ThomasDieckmann/TPL-II/photos/20220920_143919.jpg

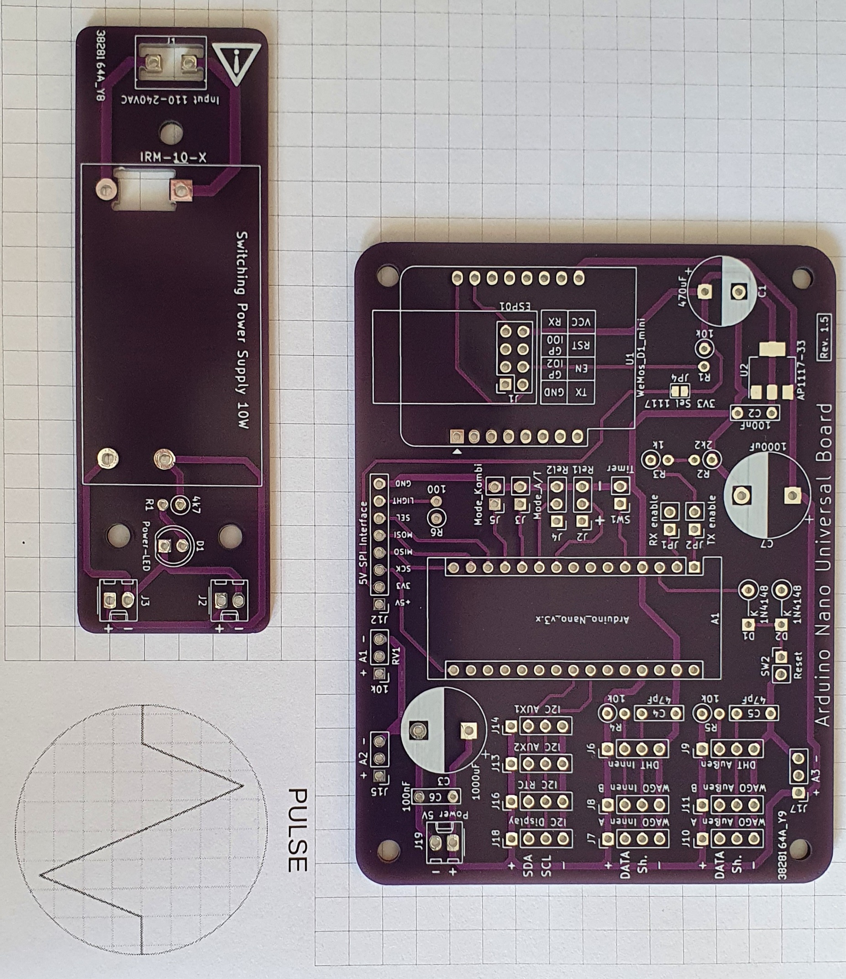
photos/20220920_143919.jpg
