ThomasDieckmann/TPL-II/photos/20221005_145727.jpg

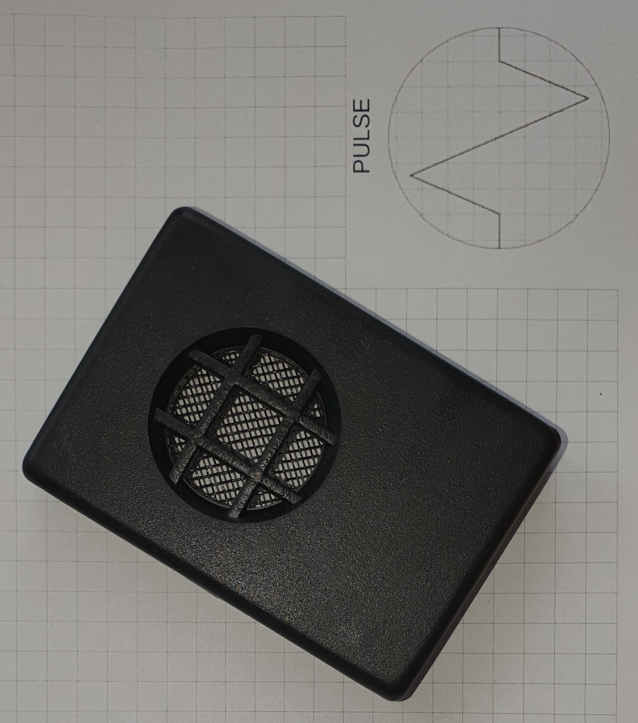
photos/20221005_145727.jpg
