ThomasDieckmann/TPL-II/photos/20221005_145737.jpg

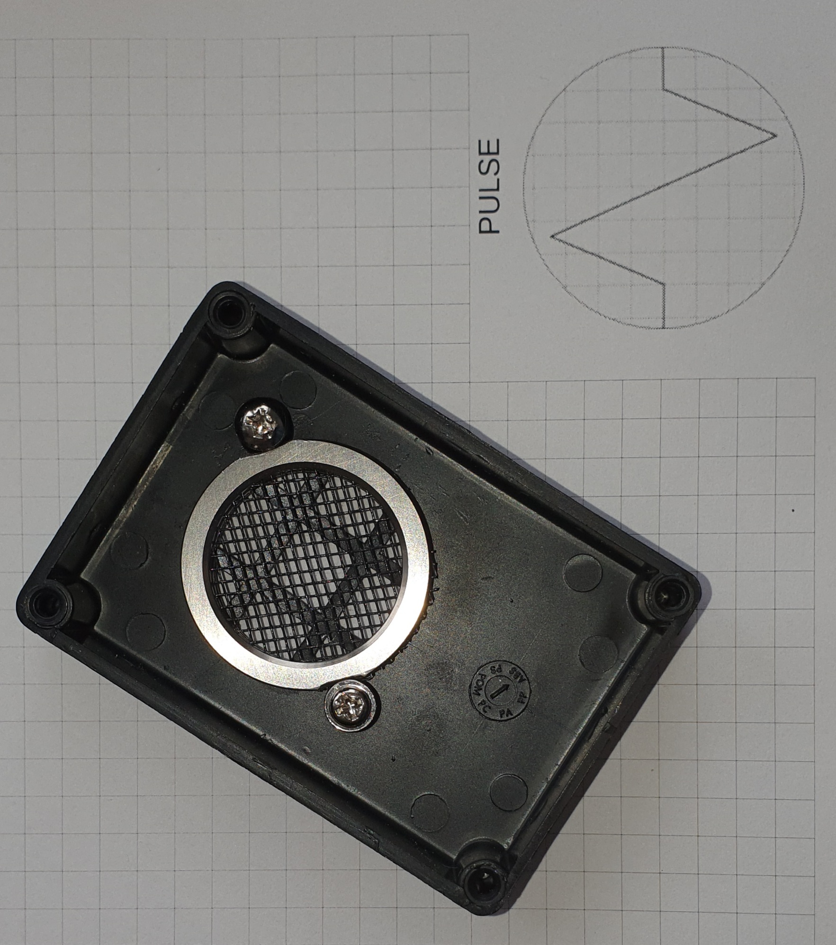
photos/20221005_145737.jpg
