ThomasDieckmann/TPL-II/photos/20221005_145815.jpg

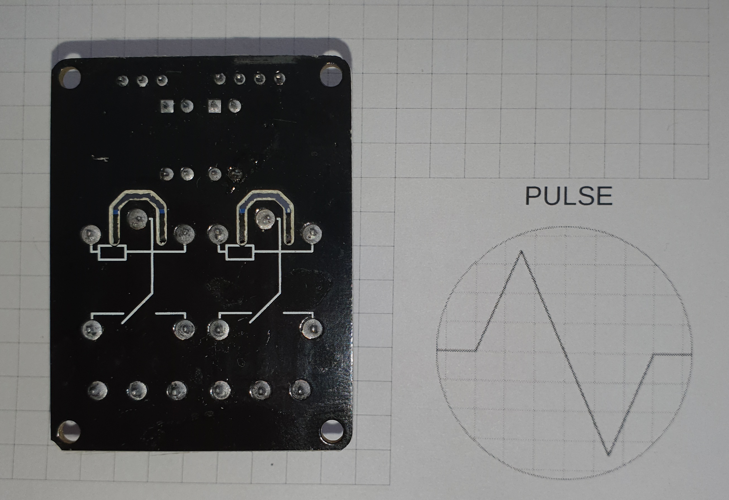
photos/20221005_145815.jpg
