ThomasDieckmann/TPL-II/photos/20221005_145848.jpg

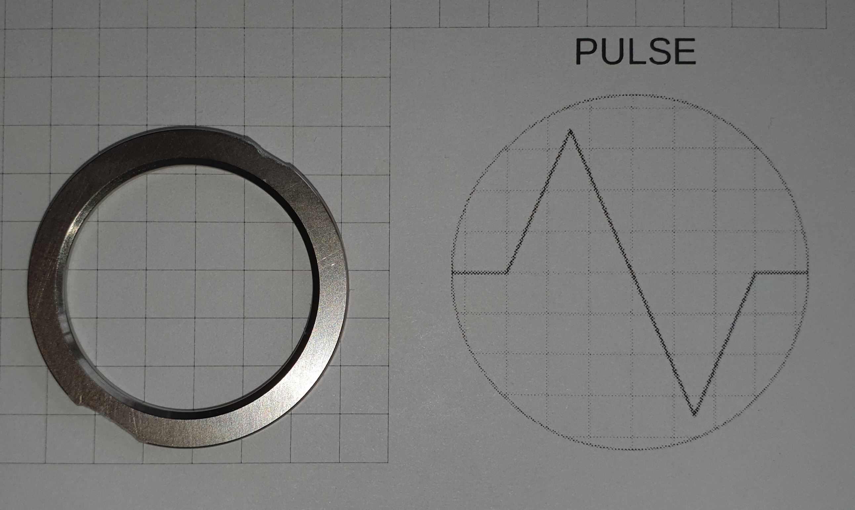
photos/20221005_145848.jpg
