ThomasDieckmann/TPL-II/photos/20221005_151055.jpg

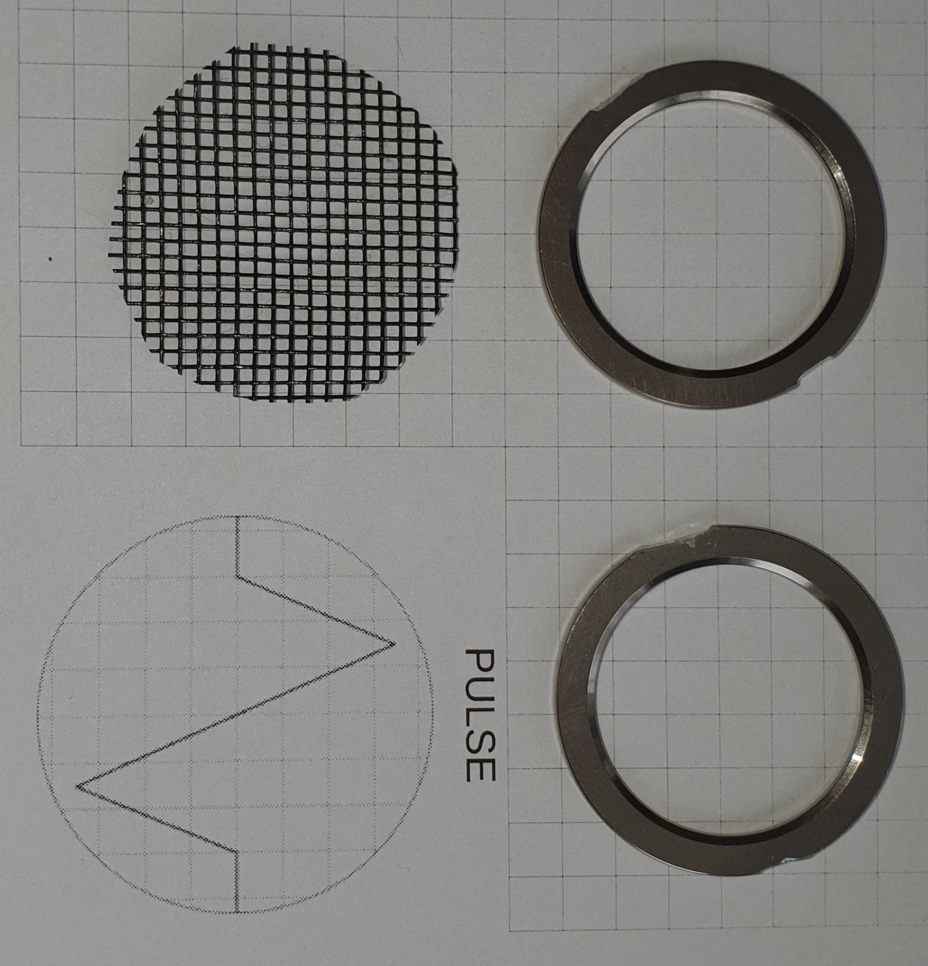
photos/20221005_151055.jpg
