ThomasDieckmann/TPL-II/photos/20221005_151303.jpg

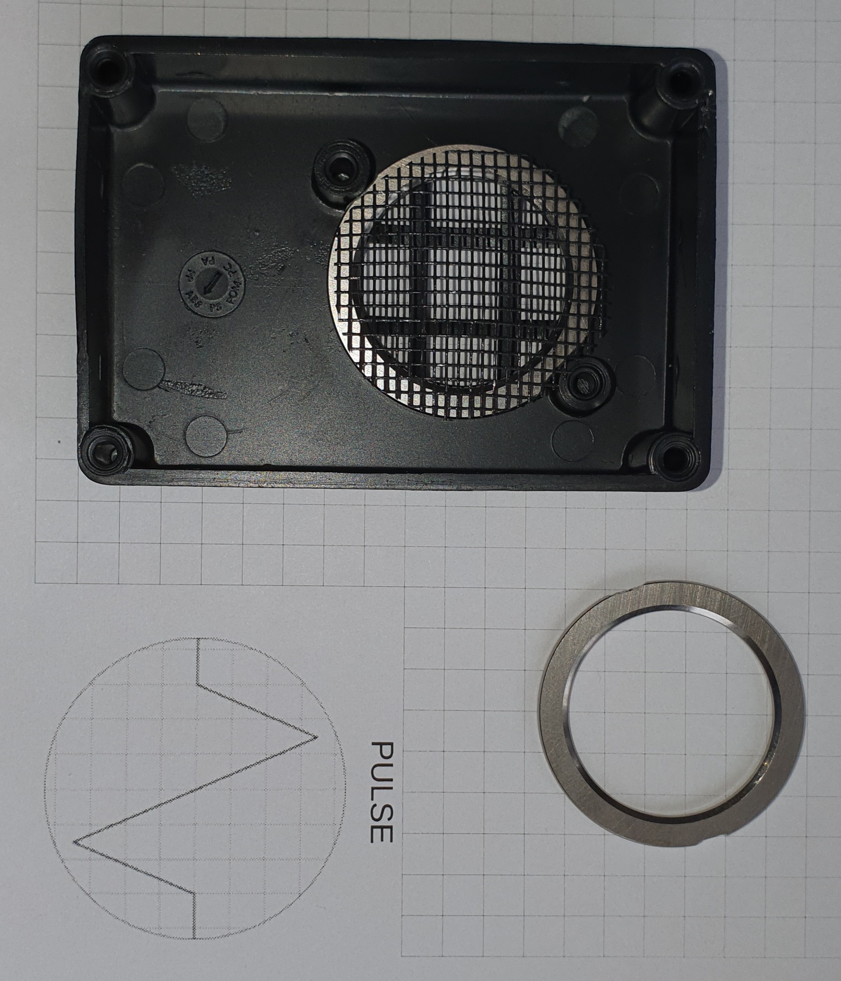
photos/20221005_151303.jpg
