ThomasDieckmann/TPL-II/photos/20221006_083249.jpg

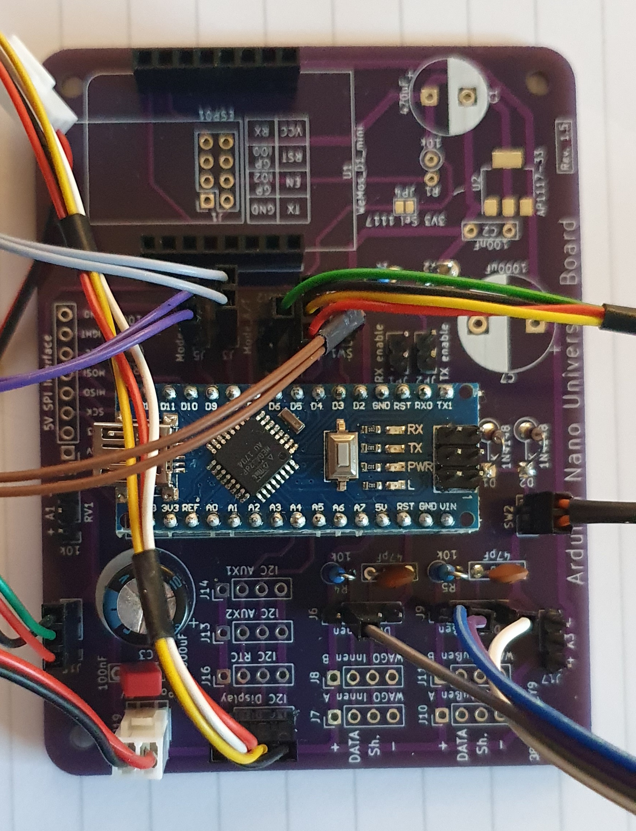
photos/20221006_083249.jpg
