ThomasDieckmann/TPL-II/photos/20221006_105342.jpg

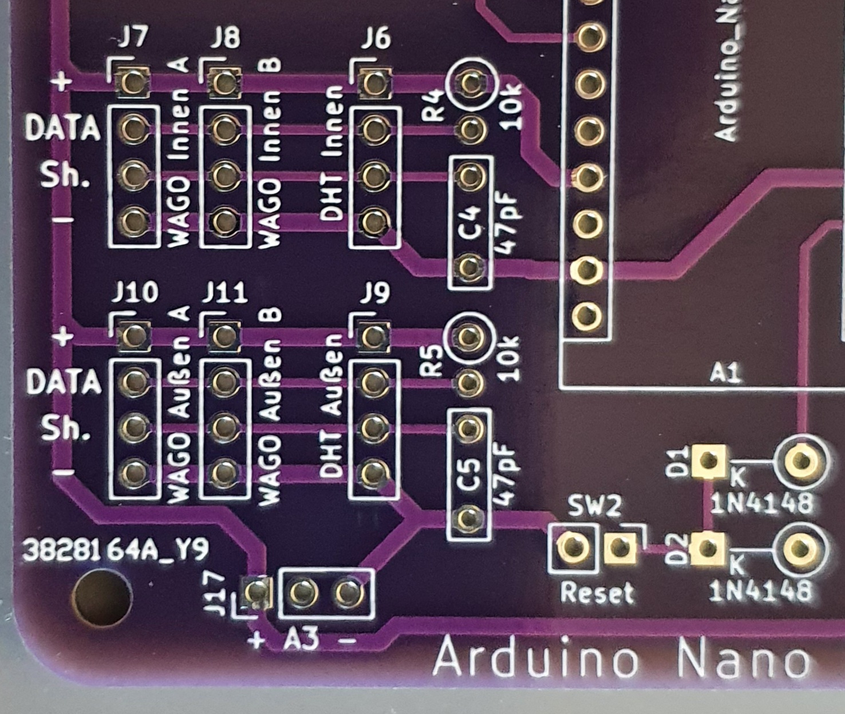
photos/20221006_105342.jpg
