ThomasDieckmann/TPL-II/photos/20221011_225733.jpg

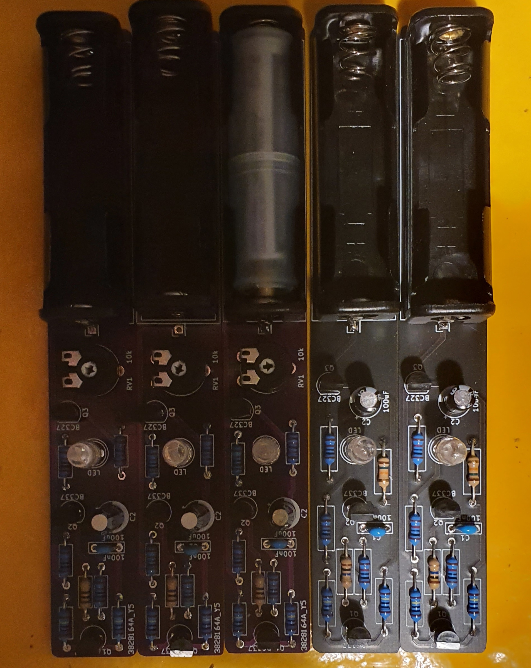
photos/20221011_225733.jpg
