ThomasDieckmann/TPL-II/photos/20221021_124702.jpg

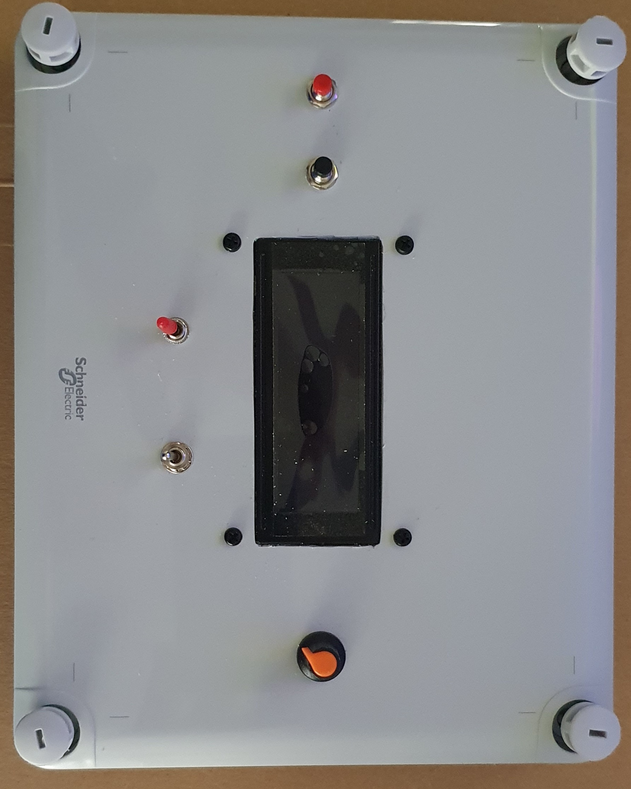
photos/20221021_124702.jpg
