ThomasDieckmann/TPL-II/photos/20221021_125103.jpg

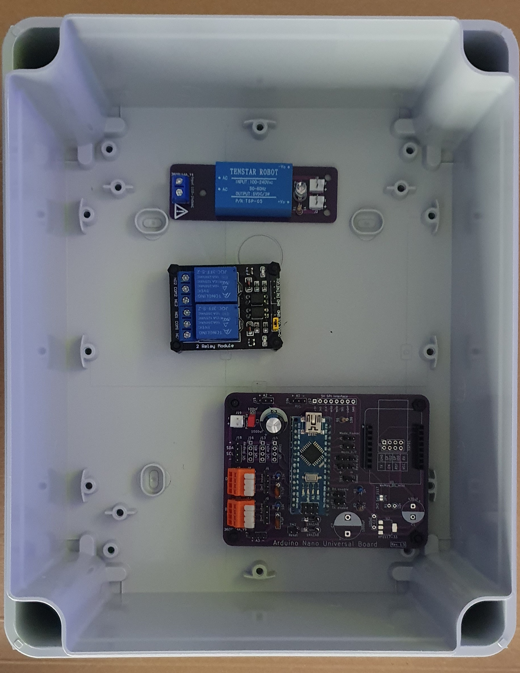
photos/20221021_125103.jpg
