ThomasDieckmann/TPL-II/photos/20221021_145954.jpg

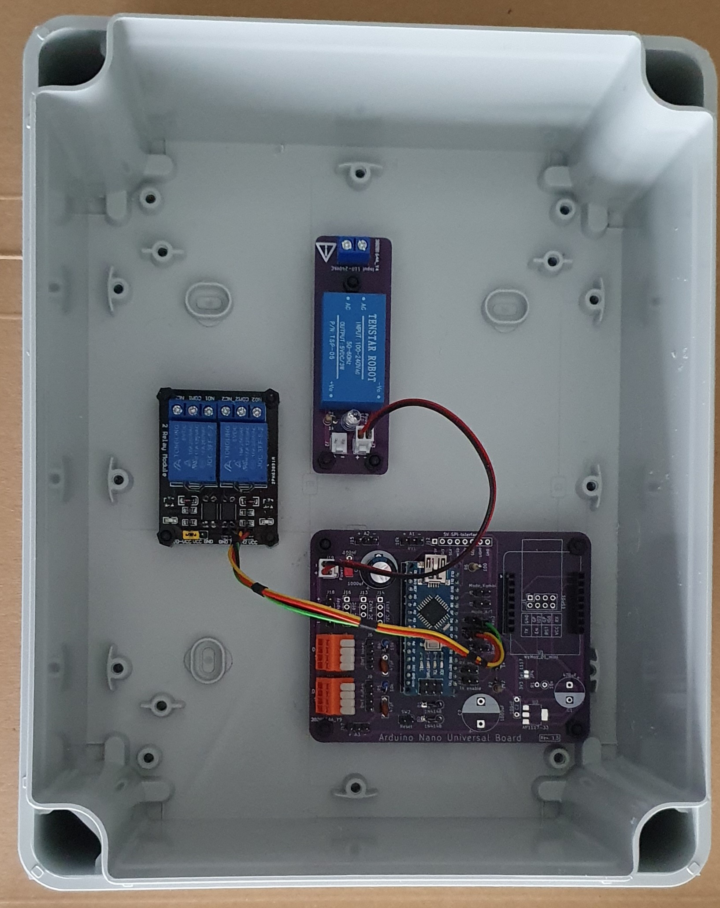
photos/20221021_145954.jpg
