ThomasDieckmann/TPL-II/photos/20221021_170227.jpg

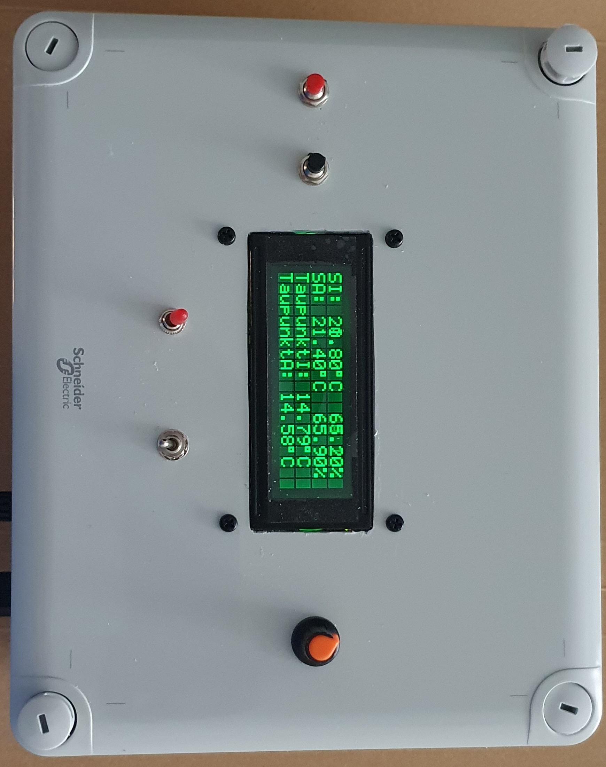
photos/20221021_170227.jpg
