ThomasDieckmann/TPL-II/photos/20221021_170622.jpg

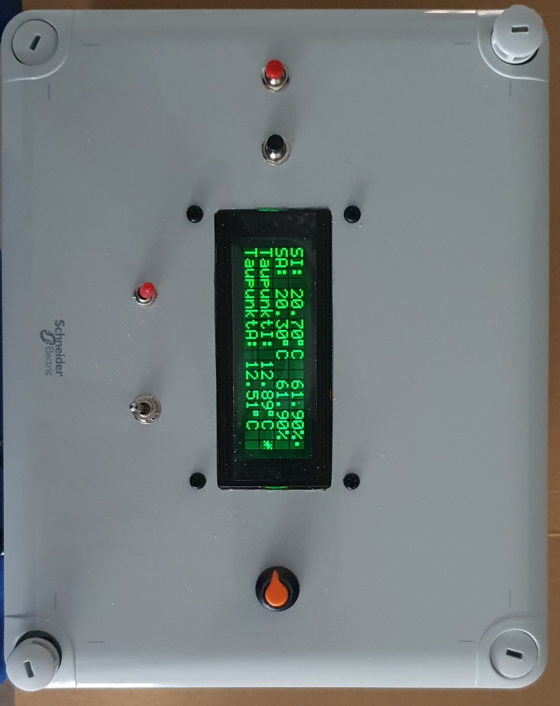
photos/20221021_170622.jpg
