ThomasDieckmann/TPL-II/photos/20221027_135438.jpg

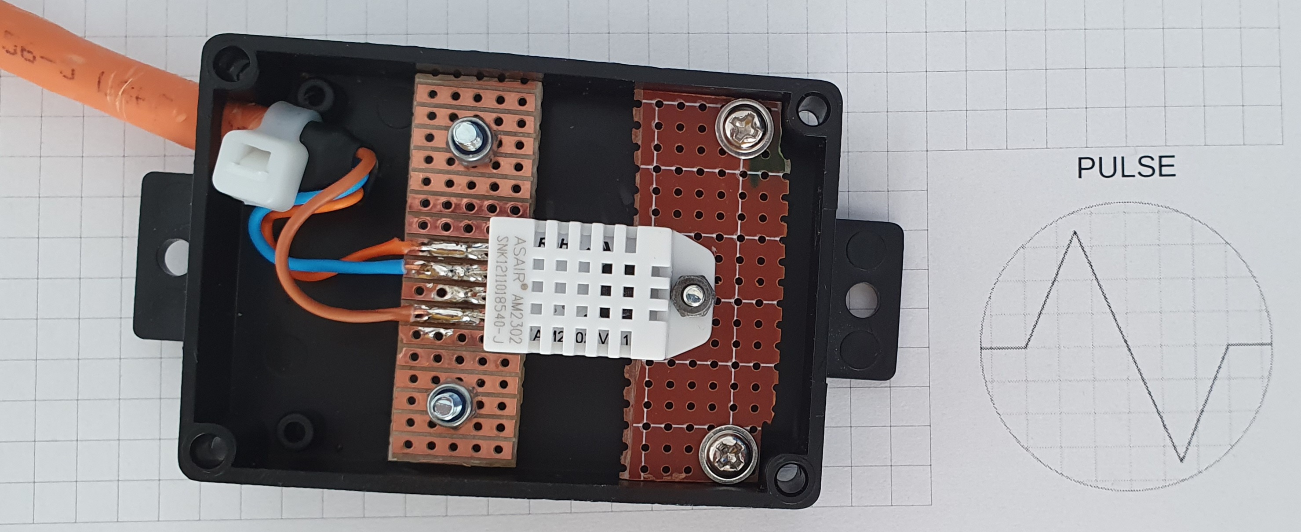
photos/20221027_135438.jpg
