ThomasDieckmann/TPL-II/photos/20221027_141711.jpg

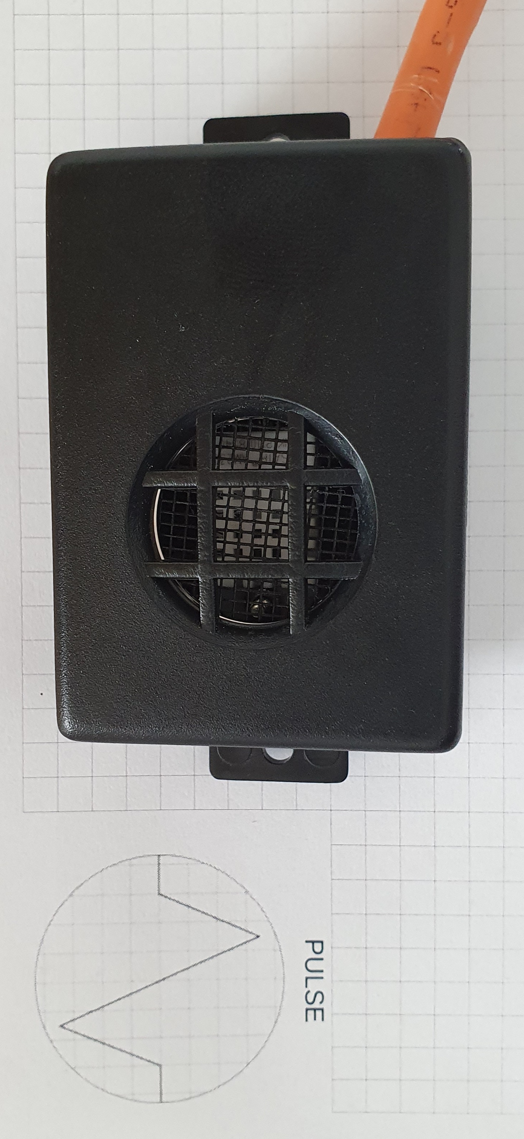
photos/20221027_141711.jpg
