ThomasDieckmann/TPL-II/photos/20221027_153632.jpg

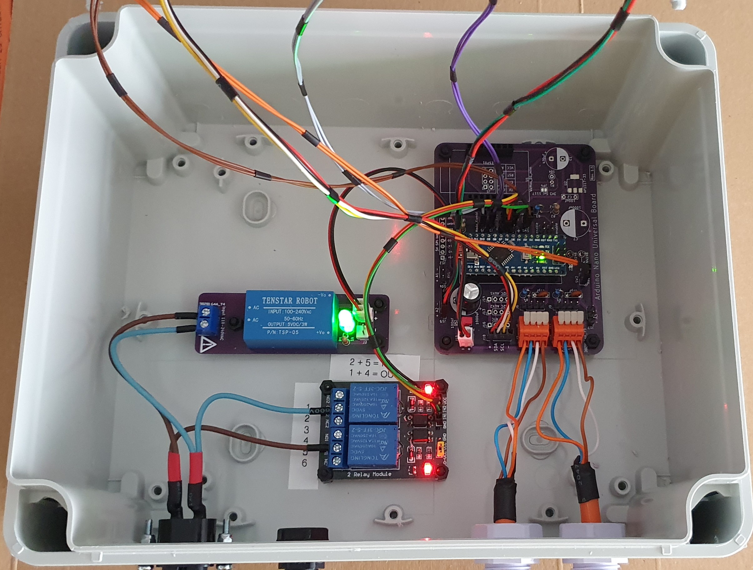
photos/20221027_153632.jpg
