ThomasDieckmann/TPL-II/photos/20221123_121524.jpg

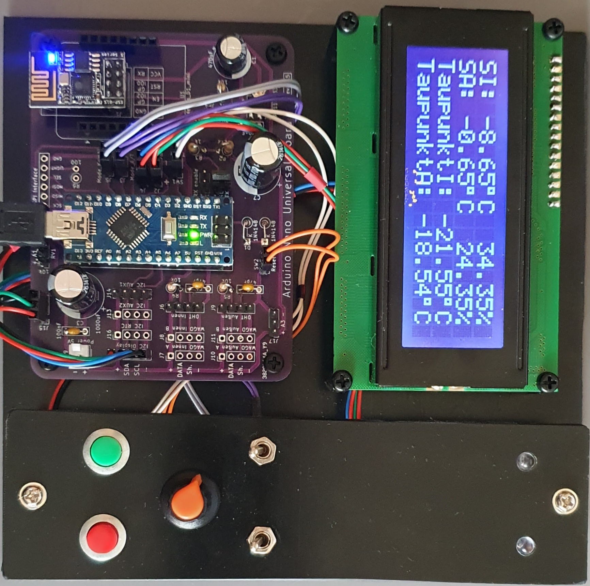
photos/20221123_121524.jpg
