ThomasDieckmann/TPL-II/photos/20231001_195801.jpg

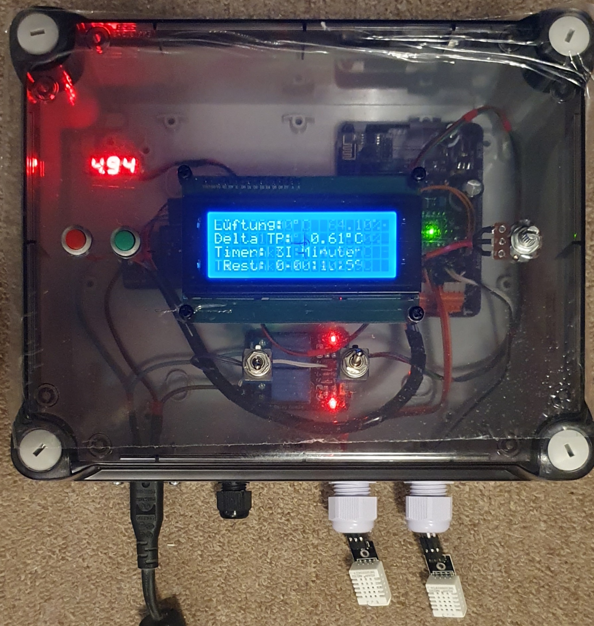
photos/20231001_195801.jpg
