ThomasDieckmann/TPL-II/photos/board.jpg

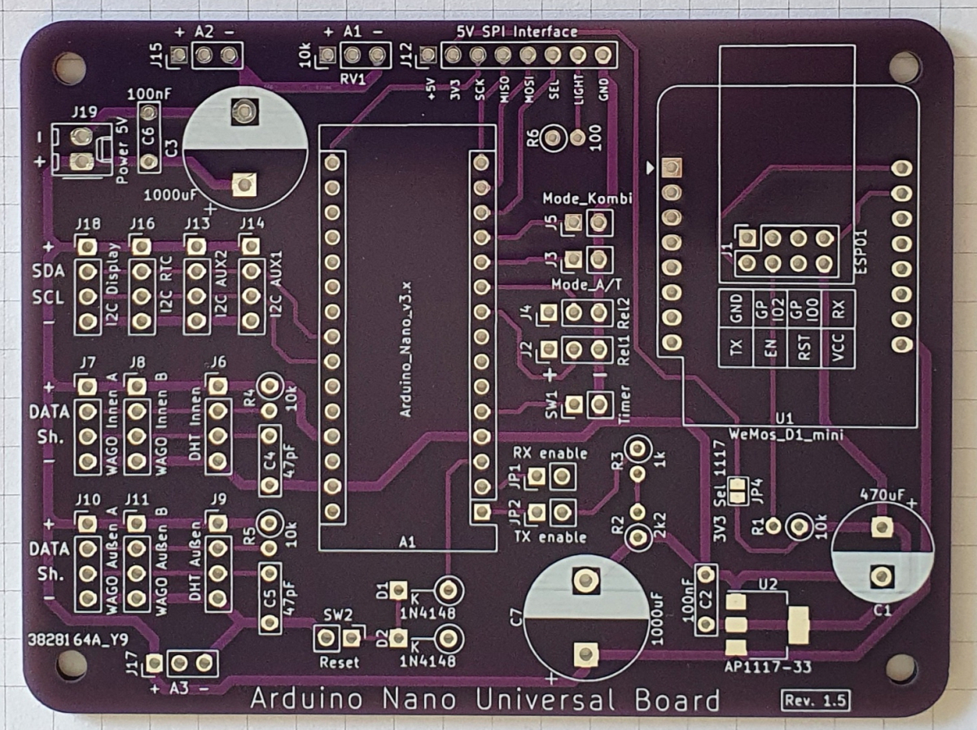
photos/board.jpg
